SystemStrategy/Hash-Thermostat/3d STL/Face.png

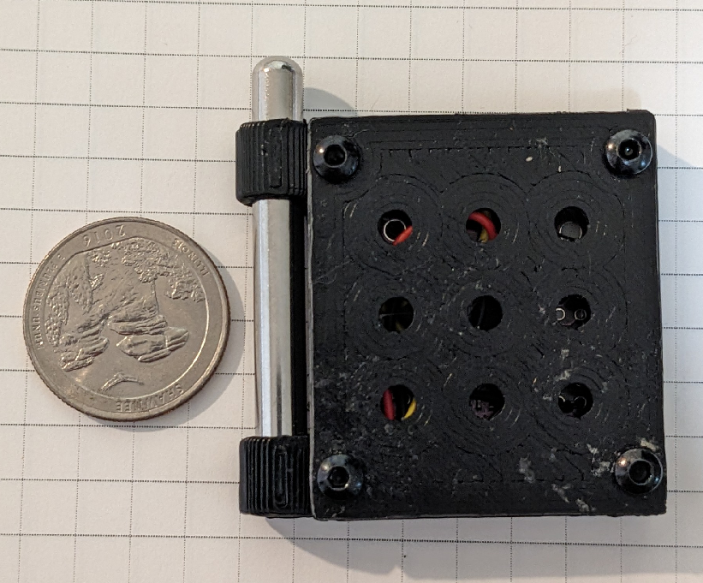
3d STL/Face.png
