SystemStrategy/Hash-Thermostat/Webpage_Images/Config.png

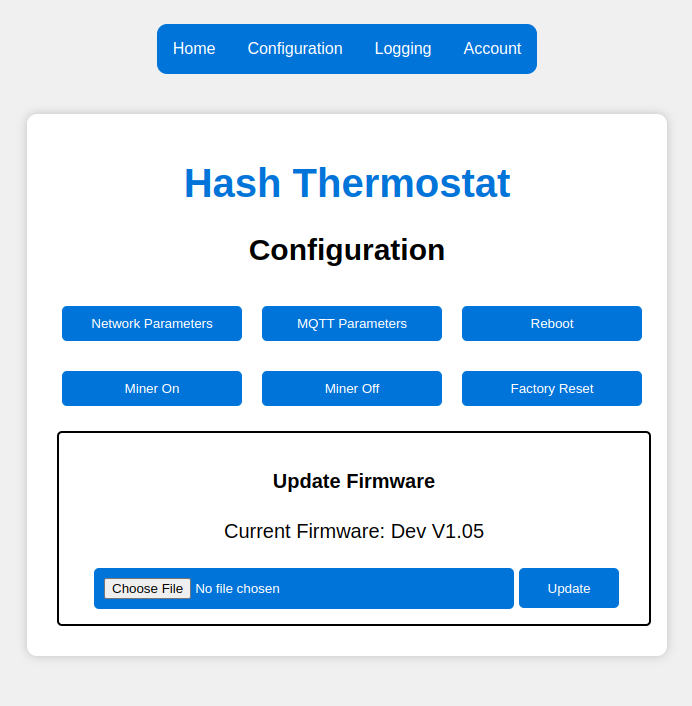
Webpage_Images/Config.png
