SystemStrategy/Hash-Thermostat/Webpage_Images/Change Login.png

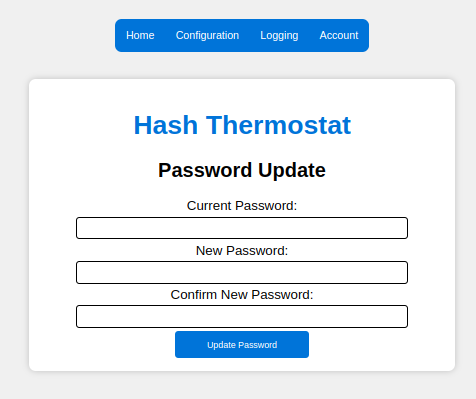
Webpage_Images/Change Login.png
